ac-rad/roboculture/src/camera_cal_imgs/2023-09-20-135940.jpg

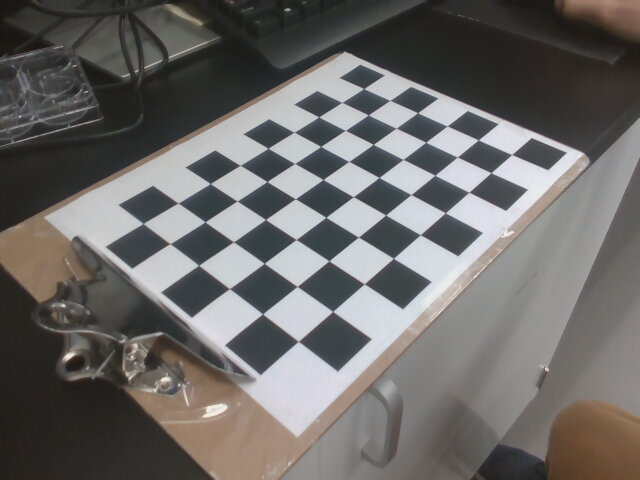
src/camera_cal_imgs/2023-09-20-135940.jpg
