ac-rad/roboculture/src/camera_cal_imgs/2023-09-20-135949.jpg

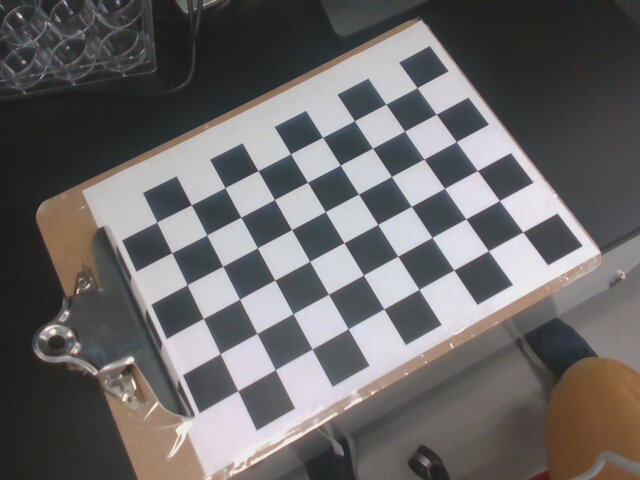
src/camera_cal_imgs/2023-09-20-135949.jpg
