ac-rad/roboculture/src/camera_cal_imgs/2023-09-20-135957.jpg

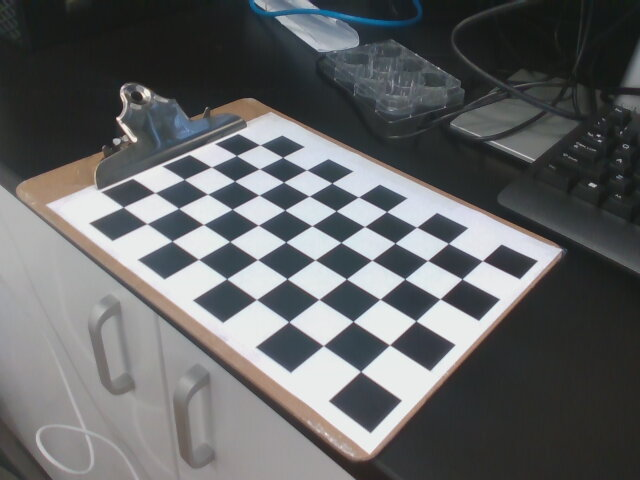
src/camera_cal_imgs/2023-09-20-135957.jpg
