ac-rad/roboculture/src/camera_cal_imgs/2023-09-20-140148.jpg

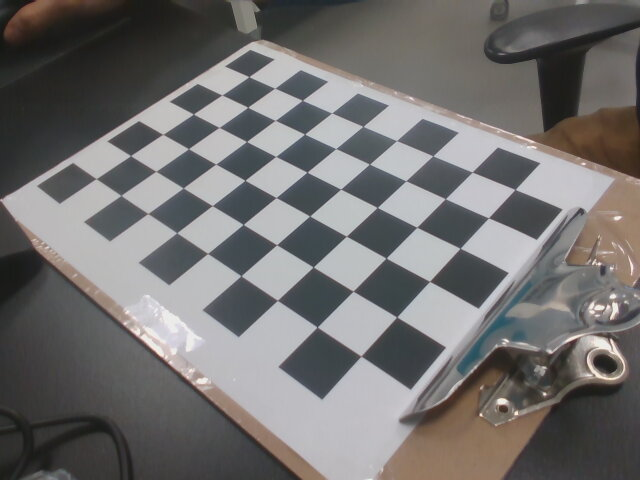
src/camera_cal_imgs/2023-09-20-140148.jpg
